SimonAnnetts/yaesu_icom_atu_seq_v2/src/button_io.h

#pragma once

// Tune button (D6, active-low: pressed pulls the pin to ground). Presses are
// debounced and logged on Serial0.

void buttonIoBegin();

// Call every loop(). True once per debounced press.
bool buttonIoPoll();
